open-bldc/open-bldc-hardware/v0.3/power/power.brd

## EAGLE design v0.3/power/power.brd (2012-07-01)

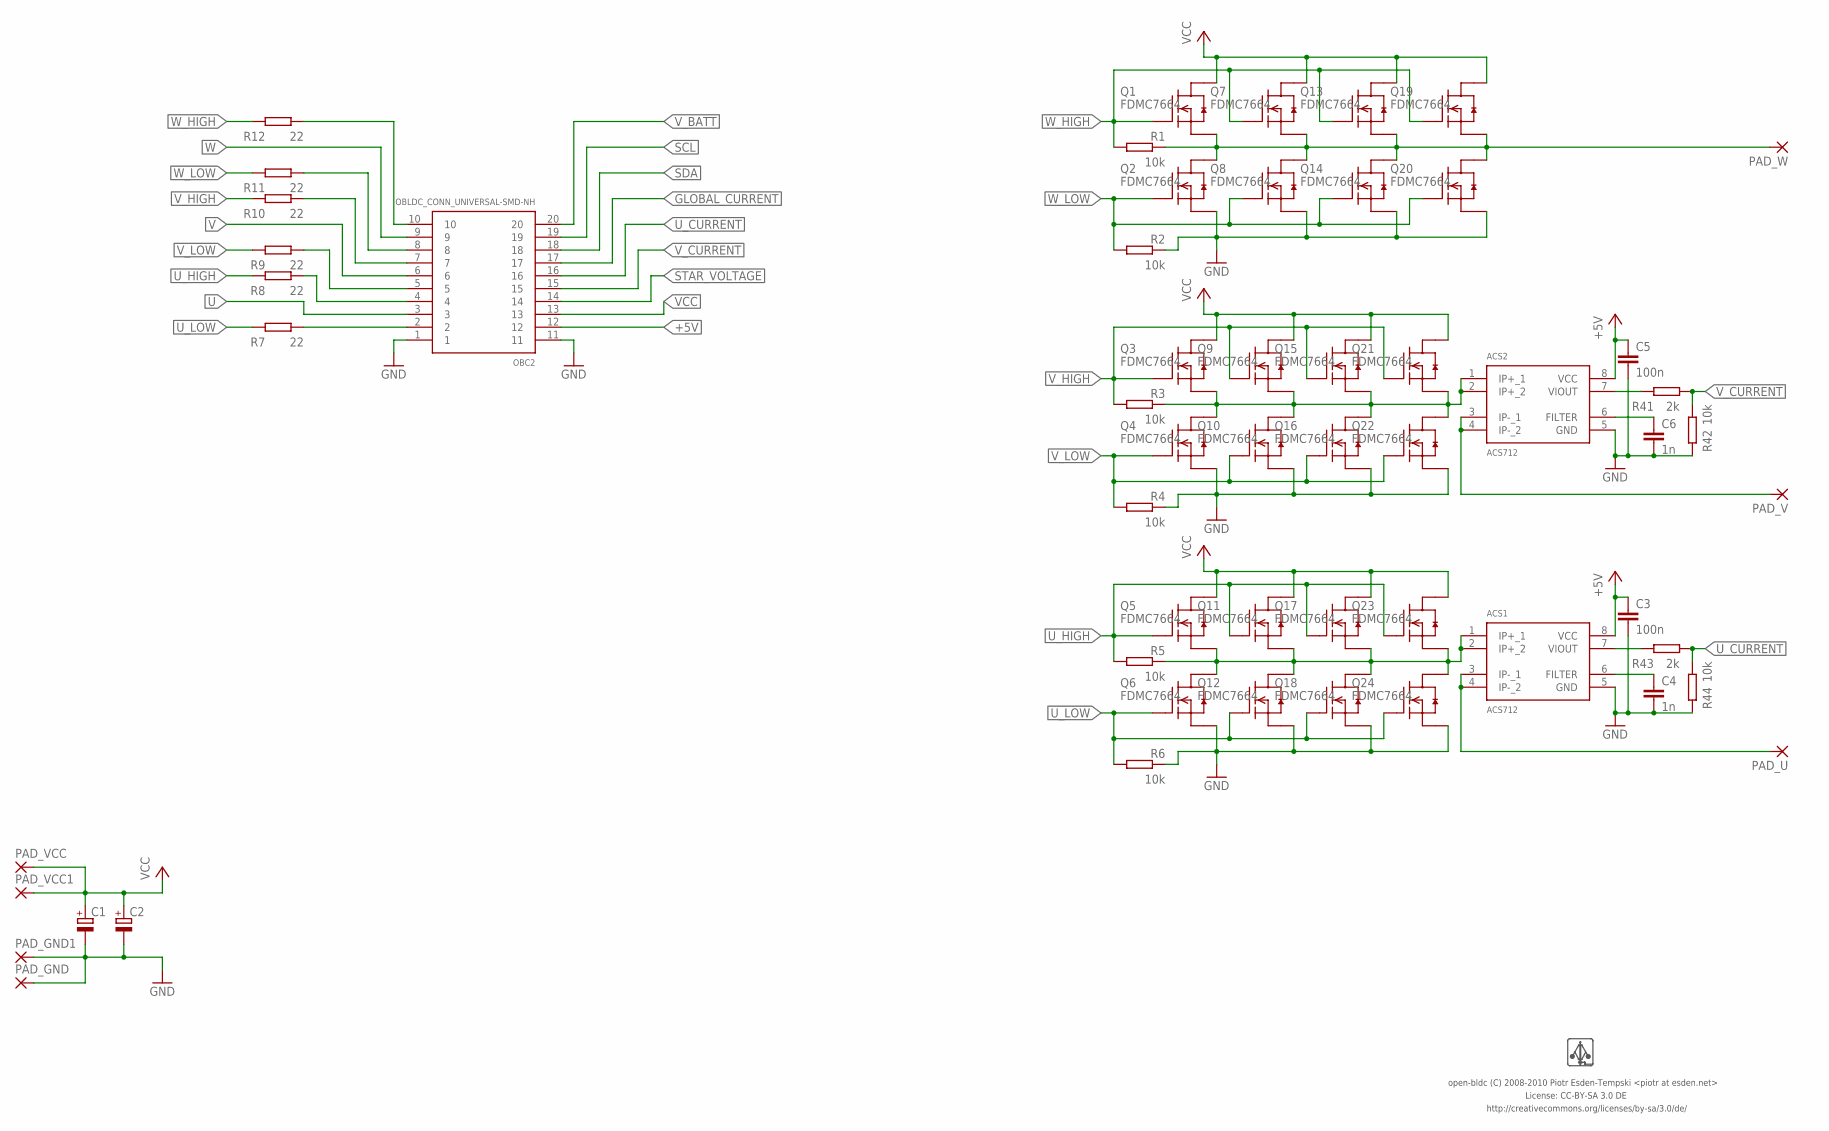
[picture p24: schematic power.sch]

Parts:
ACS1, ACS2: ACS712; SO8
C1, C2: CPOL-EUE5-10.5; E5-10,5
C3, C5: 100n; 0603-CAP
C4, C6: 1n; 0603-CAP
OBC2: OBLDC_CONN_UNIVERSAL-SMD-NH; OBLDC_CONN_SMD_NO_HOLES
PAD_GND, PAD_GND1: WIREPAD-2MM; WIREPAD_2MM
PAD_U: WIREPAD-2MM; WIREPAD_2MM
PAD_V: WIREPAD-2MM; WIREPAD_2MM
PAD_VCC, PAD_VCC1: WIREPAD-2MM; WIREPAD_2MM
PAD_W: WIREPAD-2MM; WIREPAD_2MM
Q1, Q2, Q3, Q4, Q5, Q6, Q7, Q8, Q9, Q10, Q11, Q12, Q13, Q14, Q15, Q16, Q17, Q18, Q19, Q20, Q21, Q22, Q23, Q24: FDMC7664; MLP33
R1, R2, R3, R4, R5, R6, R42, R44: 10k; 0603-RES
R7, R8, R9, R10, R11, R12: 22; 0603-RES
R41, R43: 2k; 0603-RES
U$2: LOGO-NORM; LOGO

Connections:
+5V: ACS1.8 (VCC), ACS2.8 (VCC), C3.P$1 (1), C5.P$1 (1), OBC2.12
GLOBAL_CURRENT: OBC2.17
GND: ACS1.5 (GND), ACS2.5 (GND), C1.-, C2.-, C3.P$2 (2), C4.P$2 (2), C5.P$2 (2), C6.P$2 (2), OBC2.1, OBC2.11, PAD_GND.1, PAD_GND1.1, Q2.123S (S), Q4.123S (S), Q6.123S (S), Q8.123S (S), Q10.123S (S), Q12.123S (S), Q14.123S (S), Q16.123S (S), Q18.123S (S), Q20.123S (S), Q22.123S (S), Q24.123S (S), R2.P$1 (1), R4.P$1 (1), R6.P$1 (1), R42.P$2 (2), R44.P$2 (2)
unnamed: ACS1.3 (IP-_1), ACS1.4 (IP-_2), PAD_U.1
unnamed: ACS2.6 (FILTER), C6.P$1 (1)
unnamed: ACS2.3 (IP-_1), ACS2.4 (IP-_2), PAD_V.1
unnamed: OBC2.2, R7.P$1 (1)
unnamed: OBC2.4, R8.P$1 (1)
unnamed: OBC2.5, R9.P$1 (1)
unnamed: OBC2.7, R10.P$1 (1)
unnamed: OBC2.8, R11.P$1 (1)
unnamed: OBC2.10, R12.P$1 (1)
unnamed: ACS1.6 (FILTER), C4.P$1 (1)
unnamed: ACS2.7 (VIOUT), R41.P$2 (2)
unnamed: ACS1.7 (VIOUT), R43.P$2 (2)
SCL: OBC2.19
SDA: OBC2.18
STAR_VOLTAGE: OBC2.14
U: ACS1.1 (IP+_1), ACS1.2 (IP+_2), OBC2.3, Q5.123S (S), Q6.5678D (D), Q11.123S (S), Q12.5678D (D), Q17.123S (S), Q18.5678D (D), Q23.123S (S), Q24.5678D (D), R5.P$1 (1)
U_CURRENT: OBC2.16, R43.P$1 (1), R44.P$1 (1)
U_HIGH: Q5.4G (G), Q11.4G (G), Q17.4G (G), Q23.4G (G), R5.P$2 (2), R8.P$2 (2)
U_LOW: Q6.4G (G), Q12.4G (G), Q18.4G (G), Q24.4G (G), R6.P$2 (2), R7.P$2 (2)
V: ACS2.1 (IP+_1), ACS2.2 (IP+_2), OBC2.6, Q3.123S (S), Q4.5678D (D), Q9.123S (S), Q10.5678D (D), Q15.123S (S), Q16.5678D (D), Q21.123S (S), Q22.5678D (D), R3.P$1 (1)
VCC: C1.+, C2.+, OBC2.13, PAD_VCC.1, PAD_VCC1.1, Q1.5678D (D), Q3.5678D (D), Q5.5678D (D), Q7.5678D (D), Q9.5678D (D), Q11.5678D (D), Q13.5678D (D), Q15.5678D (D), Q17.5678D (D), Q19.5678D (D), Q21.5678D (D), Q23.5678D (D)
V_BATT: OBC2.20
V_CURRENT: OBC2.15, R41.P$1 (1), R42.P$1 (1)
V_HIGH: Q3.4G (G), Q9.4G (G), Q15.4G (G), Q21.4G (G), R3.P$2 (2), R10.P$2 (2)
V_LOW: Q4.4G (G), Q10.4G (G), Q16.4G (G), Q22.4G (G), R4.P$2 (2), R9.P$2 (2)
W: OBC2.9, PAD_W.1, Q1.123S (S), Q2.5678D (D), Q7.123S (S), Q8.5678D (D), Q13.123S (S), Q14.5678D (D), Q19.123S (S), Q20.5678D (D), R1.P$1 (1)
W_HIGH: Q1.4G (G), Q7.4G (G), Q13.4G (G), Q19.4G (G), R1.P$2 (2), R12.P$2 (2)
W_LOW: Q2.4G (G), Q8.4G (G), Q14.4G (G), Q20.4G (G), R2.P$2 (2), R11.P$2 (2)

Notes on the sheet:
License: CC-BY-SA 3.0 DE
http://creativecommons.org/licenses/by-sa/3.0/de/
open-bldc (C) 2008-2010 Piotr Esden-Tempski <piotr at esden.net>

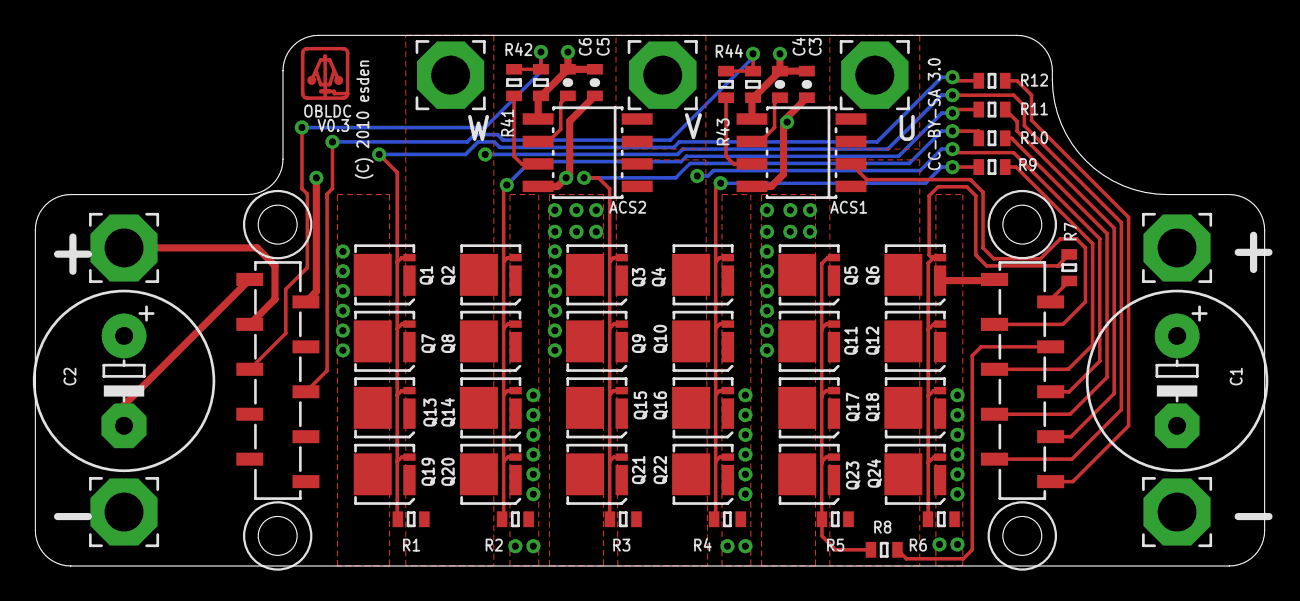
[picture p25: board power.brd from above]

Board: 4 copper layers, 69.5 x 30.0 mm, 58 parts (0 on the bottom side), 26 nets.

Other parts of the board:
U$1: OBLDC_MECH
