open-bldc/open-bldc-hardware/onepiece/v0.1/onepiece.brd

## EAGLE design onepiece/v0.1/onepiece.brd (2012-07-01)

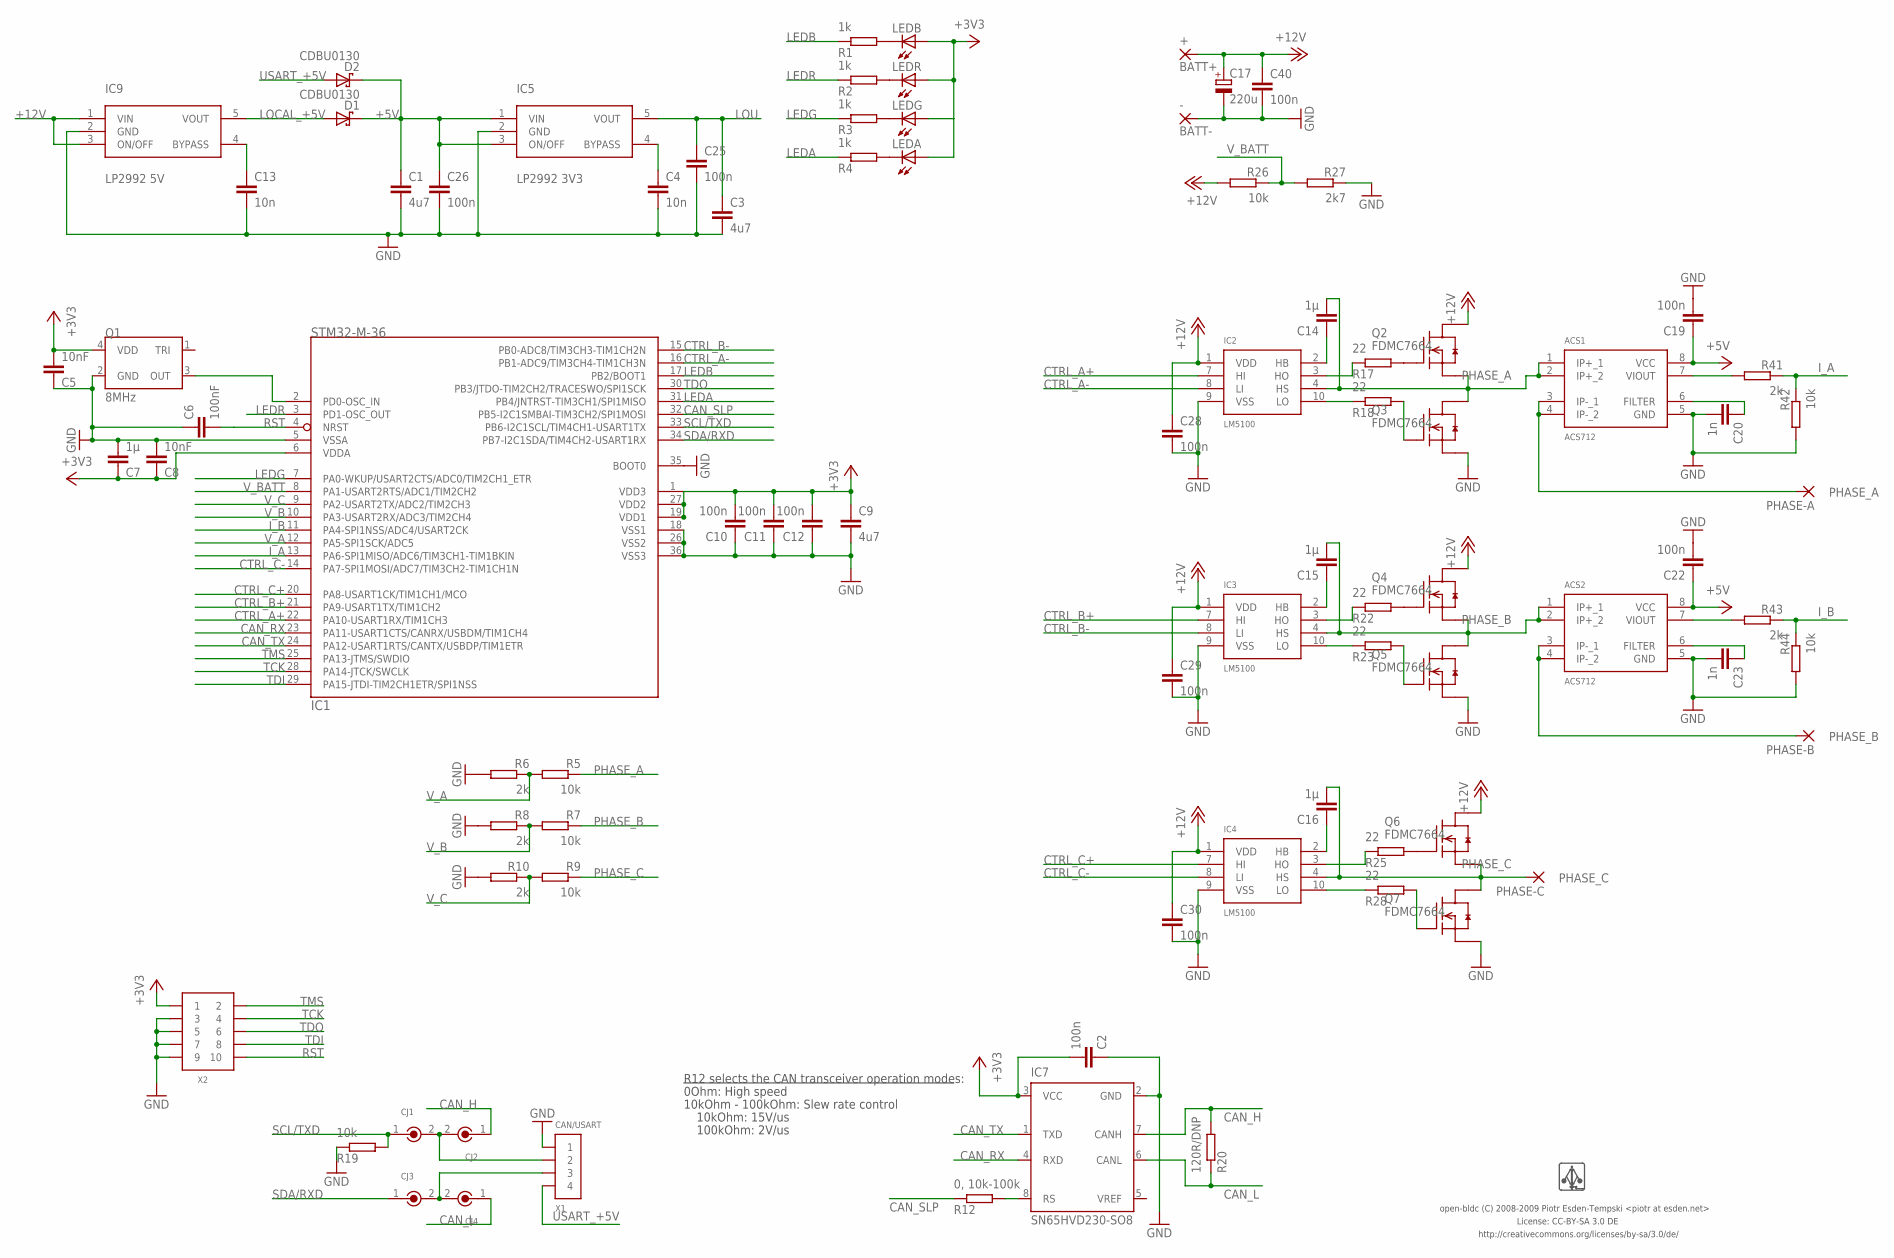
[picture p26: schematic onepiece.sch]

Parts:
+: BATT+; SMD2,54-5,08
-: BATT-; SMD2,54-5,08
ACS1, ACS2: ACS712; SO8
C1, C3, C9: 4u7; 0603-CAP
C2, C10, C11, C12, C19, C22, C25, C26, C28, C29, C30, C40: 100n; 0603-CAP
C4, C13: 10n; 0603-CAP
C5, C8: 10nF; 0603-CAP
C6: 100nF; 0603-CAP
C7, C14, C15, C16: 1µ; 0603-CAP
C17: 220u; 7343/D
C20, C23: 1n; 0603-CAP
CJ1, CJ2, CJ3, CJ4: CIRC_JMP
D1, D2: CDBU0130; 0603-LED
IC1: STM32-M-36; VFQFPN36-LP
IC2, IC3, IC4: LM5100; LLP-10
IC5: LP2992 3V3; SOT23-5
IC7: SN65HVD230-SO8; SO8
IC9: LP2992 5V; SOT23-5
LEDA: AMBER; 0603-LED
LEDB: BLUE; 0603-LED
LEDG: GREEN; 0603-LED
LEDR: RED; 0603-LED
PHASE-A: PHASE_A; SMD2,54-5,08
PHASE-B: PHASE_B; SMD2,54-5,08
PHASE-C: PHASE_C; SMD2,54-5,08
Q1: 8MHz; ASE_OSCILLATOR
Q2, Q3, Q4, Q5, Q6, Q7: FDMC7664; MLP33
R1, R2, R3, R4: 1k; 0603-RES
R5, R7, R9, R19, R26, R42, R44: 10k; 0603-RES
R6, R8, R10, R41, R43: 2k; 0603-RES
R12: 0, 10k-100k; 0603-RES
R17, R18, R22, R23, R25, R28: 22; 0603-RES
R20: 120R/DNP; 0603-RES
R27: 2k7; 0603-RES
U$1: LOGO; LOGO_SMALL
X1: CAN/USART; PB-53261-04
X2: PIN_HDR_EDG_1.27MM_5-2; PIN_HDR_1.27MM_SMD_DH_10

Connections:
+5V: ACS1.8 (VCC), ACS2.8 (VCC), C1.P$1 (1), C19.P$1 (1), C22.P$1 (1), C26.P$1 (1), D1.C, D2.C, IC5.1 (VIN), IC5.3 (ON/OFF)
+12V: +.1, C17.+, C28.P$1 (1), C29.P$1 (1), C30.P$1 (1), C40.P$1 (1), IC2.1 (VDD), IC3.1 (VDD), IC4.1 (VDD), IC9.1 (VIN), IC9.3 (ON/OFF), Q2.5678D (D), Q4.5678D (D), Q6.5678D (D), R26.P$2 (2)
CAN_H: CJ2.1, IC7.7 (CANH), R20.P$2 (2)
CAN_L: CJ4.1, IC7.6 (CANL), R20.P$1 (1)
CAN_RX: IC1.23 (PA11-USART1CTS/CANRX/USBDM/TIM1CH4), IC7.4 (RXD)
CAN_SLP: IC1.32 (PB5-I2C1SMBAI-TIM3CH2/SPI1MOSI), R12.P$1 (1)
CAN_TX: IC1.24 (PA12-USART1RTS/CANTX/USBDP/TIM1ETR), IC7.1 (TXD)
CTRL_A+: IC1.22 (PA10-USART1RX/TIM1CH3), IC2.7 (HI)
CTRL_A-: IC1.16 (PB1-ADC9/TIM3CH4-TIM1CH3N), IC2.8 (LI)
CTRL_B+: IC1.21 (PA9-USART1TX/TIM1CH2), IC3.7 (HI)
CTRL_B-: IC1.15 (PB0-ADC8/TIM3CH3-TIM1CH2N), IC3.8 (LI)
CTRL_C+: IC1.20 (PA8-USART1CK/TIM1CH1/MCO), IC4.7 (HI)
CTRL_C-: IC1.14 (PA7-SPI1MOSI/ADC7/TIM3CH2-TIM1CH1N), IC4.8 (LI)
GND: -.1, ACS1.5 (GND), ACS2.5 (GND), C1.P$2 (2), C2.P$1 (1), C3.P$2 (2), C4.P$2 (2), C5.P$1 (1), C6.P$1 (1), C7.P$2 (2), C8.P$2 (2), C9.P$2 (2), C10.P$1 (1), C11.P$1 (1), C12.P$1 (1), C13.P$2 (2), C17.-, C19.P$2 (2), C20.P$2 (2), C22.P$2 (2), C23.P$2 (2), C25.P$2 (2), C26.P$2 (2), C28.P$2 (2), C29.P$2 (2), C30.P$2 (2), C40.P$2 (2), IC1.5 (VSSA), IC1.18 (VSS1), IC1.26 (VSS2), IC1.35 (BOOT0), IC1.36 (VSS3), IC2.9 (VSS), IC3.9 (VSS), IC4.9 (VSS), IC5.2 (GND), IC7.2 (GND), IC9.2 (GND), Q1.2 (GND), Q3.123S (S), Q5.123S (S), Q7.123S (S), R6.P$2 (2), R8.P$2 (2), R10.P$2 (2), R19.P$1 (1), R27.P$1 (1), R42.P$2 (2), R44.P$2 (2), X1.1, X2.3, X2.5, X2.7, X2.9
I_A: IC1.13 (PA6-SPI1MISO/ADC6/TIM3CH1-TIM1BKIN), R41.P$1 (1), R42.P$1 (1)
I_B: IC1.11 (PA4-SPI1NSS/ADC4/USART2CK), R43.P$1 (1), R44.P$1 (1)
I_PHASE_A: ACS1.3 (IP-_1), ACS1.4 (IP-_2), PHASE-A.1
I_PHASE_B: ACS2.3 (IP-_1), ACS2.4 (IP-_2), PHASE-B.1
LEDA: IC1.31 (PB4/JNTRST-TIM3CH1/SPI1MISO), R4.P$1 (1)
LEDB: IC1.17 (PB2/BOOT1), R1.P$1 (1)
LEDG: IC1.7 (PA0-WKUP/USART2CTS/ADC0/TIM2CH1_ETR), R3.P$1 (1)
LEDR: IC1.3 (PD1-OSC_OUT), R2.P$1 (1)
LOCAL_+5V: D1.A, IC9.5 (VOUT)
LOU: C2.P$2 (2), C3.P$1 (1), C5.P$2 (2), C7.P$1 (1), C8.P$1 (1), C9.P$1 (1), C10.P$2 (2), C11.P$2 (2), C12.P$2 (2), C25.P$1 (1), IC1.1 (VDD3), IC1.6 (VDDA), IC1.19 (VDD1), IC1.27 (VDD2), IC5.5 (VOUT), IC7.3 (VCC), LEDA.A, LEDB.A, LEDG.A, LEDR.A, Q1.4 (VDD), X2.1
unnamed: IC3.3 (HO), R22.P$1 (1)
unnamed: IC2.3 (HO), R17.P$1 (1)
unnamed: LEDB.C, R1.P$2 (2)
unnamed: C4.P$1 (1), IC5.4 (BYPASS)
unnamed: LEDG.C, R3.P$2 (2)
unnamed: C13.P$1 (1), IC9.4 (BYPASS)
unnamed: IC2.10 (LO), R18.P$1 (1)
unnamed: IC7.8 (RS), R12.P$2 (2)
unnamed: CJ3.2, CJ4.2, X1.3
unnamed: LEDR.C, R2.P$2 (2)
unnamed: Q2.4G (G), R17.P$2 (2)
unnamed: C14.P$1 (1), IC2.2 (HB)
unnamed: IC3.10 (LO), R23.P$1 (1)
unnamed: Q4.4G (G), R22.P$2 (2)
unnamed: Q6.4G (G), R25.P$2 (2)
unnamed: C15.P$1 (1), IC3.2 (HB)
unnamed: Q5.4G (G), R23.P$2 (2)
unnamed: IC4.3 (HO), R25.P$1 (1)
unnamed: IC4.10 (LO), R28.P$1 (1)
unnamed: C16.P$1 (1), IC4.2 (HB)
unnamed: LEDA.C, R4.P$2 (2)
unnamed: CJ1.2, CJ2.2, X1.2
unnamed: Q7.4G (G), R28.P$2 (2)
unnamed: ACS1.6 (FILTER), C20.P$1 (1)
unnamed: ACS1.7 (VIOUT), R41.P$2 (2)
unnamed: ACS2.6 (FILTER), C23.P$1 (1)
unnamed: ACS2.7 (VIOUT), R43.P$2 (2)
unnamed: IC1.2 (PD0-OSC_IN), Q1.3 (OUT)
unnamed: Q3.4G (G), R18.P$2 (2)
PHASE_A: ACS1.1 (IP+_1), ACS1.2 (IP+_2), C14.P$2 (2), IC2.4 (HS), Q2.123S (S), Q3.5678D (D), R5.P$1 (1)
PHASE_B: ACS2.1 (IP+_1), ACS2.2 (IP+_2), C15.P$2 (2), IC3.4 (HS), Q4.123S (S), Q5.5678D (D), R7.P$1 (1)
PHASE_C: C16.P$2 (2), IC4.4 (HS), PHASE-C.1, Q6.123S (S), Q7.5678D (D), R9.P$1 (1)
RST: C6.P$2 (2), IC1.4 (NRST), X2.10
SCL/TXD: CJ1.1, IC1.33 (PB6-I2C1SCL/TIM4CH1-USART1TX), R19.P$2 (2)
SDA/RXD: CJ3.1, IC1.34 (PB7-I2C1SDA/TIM4CH2-USART1RX)
TCK: IC1.28 (PA14-JTCK/SWCLK), X2.4
TDI: IC1.29 (PA15-JTDI-TIM2CH1ETR/SPI1NSS), X2.8
TDO: IC1.30 (PB3/JTDO-TIM2CH2/TRACESWO/SPI1SCK), X2.6
TMS: IC1.25 (PA13-JTMS/SWDIO), X2.2
USART_+5V: D2.A, X1.4
V_A: IC1.12 (PA5-SPI1SCK/ADC5), R5.P$2 (2), R6.P$1 (1)
V_B: IC1.10 (PA3-USART2RX/ADC3/TIM2CH4), R7.P$2 (2), R8.P$1 (1)
V_BATT: IC1.8 (PA1-USART2RTS/ADC1/TIM2CH2), R26.P$1 (1), R27.P$2 (2)
V_C: IC1.9 (PA2-USART2TX/ADC2/TIM2CH3), R9.P$2 (2), R10.P$1 (1)

Notes on the sheet:
License: CC-BY-SA 3.0 DE
http://creativecommons.org/licenses/by-sa/3.0/de/
open-bldc (C) 2008-2009 Piotr Esden-Tempski <piotr at esden.net>
R12 selects the CAN transceiver operation modes:
0Ohm: High speed
10kOhm - 100kOhm: Slew rate control
10kOhm: 15V/us
100kOhm: 2V/us

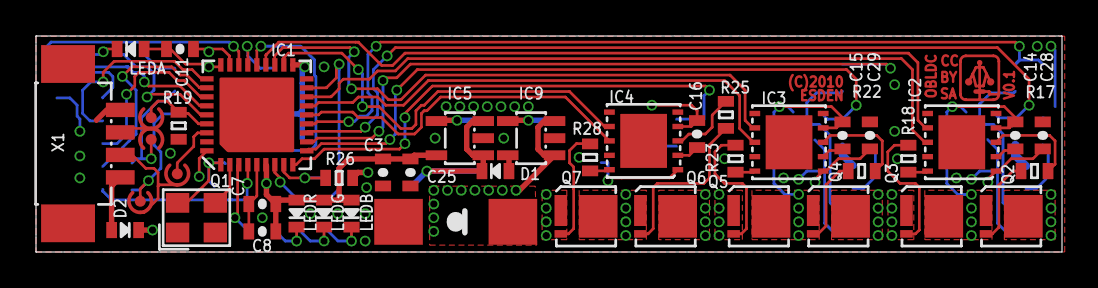
[picture p27: board onepiece.brd from above]

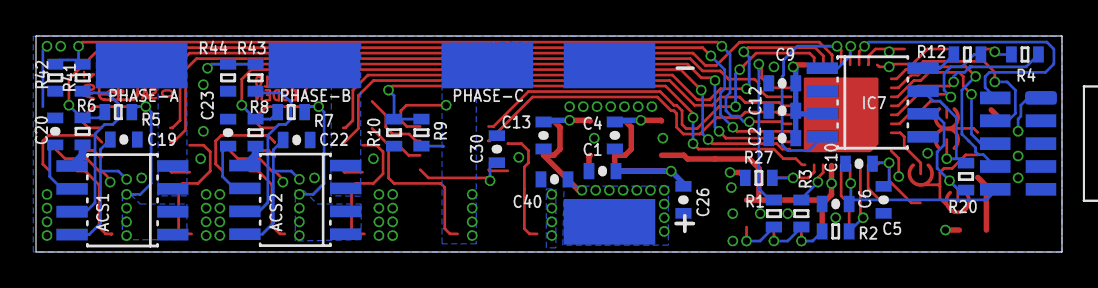
[picture p28: board onepiece.brd from below]

Board: 4 copper layers, 57.0 x 12.0 mm, 86 parts (42 on the bottom side), 68 nets.
