open-bldc/open-bldc-hardware/v0.3/power_driver/power_driver.brd

## EAGLE design v0.3/power_driver/power_driver.brd (2012-07-01)

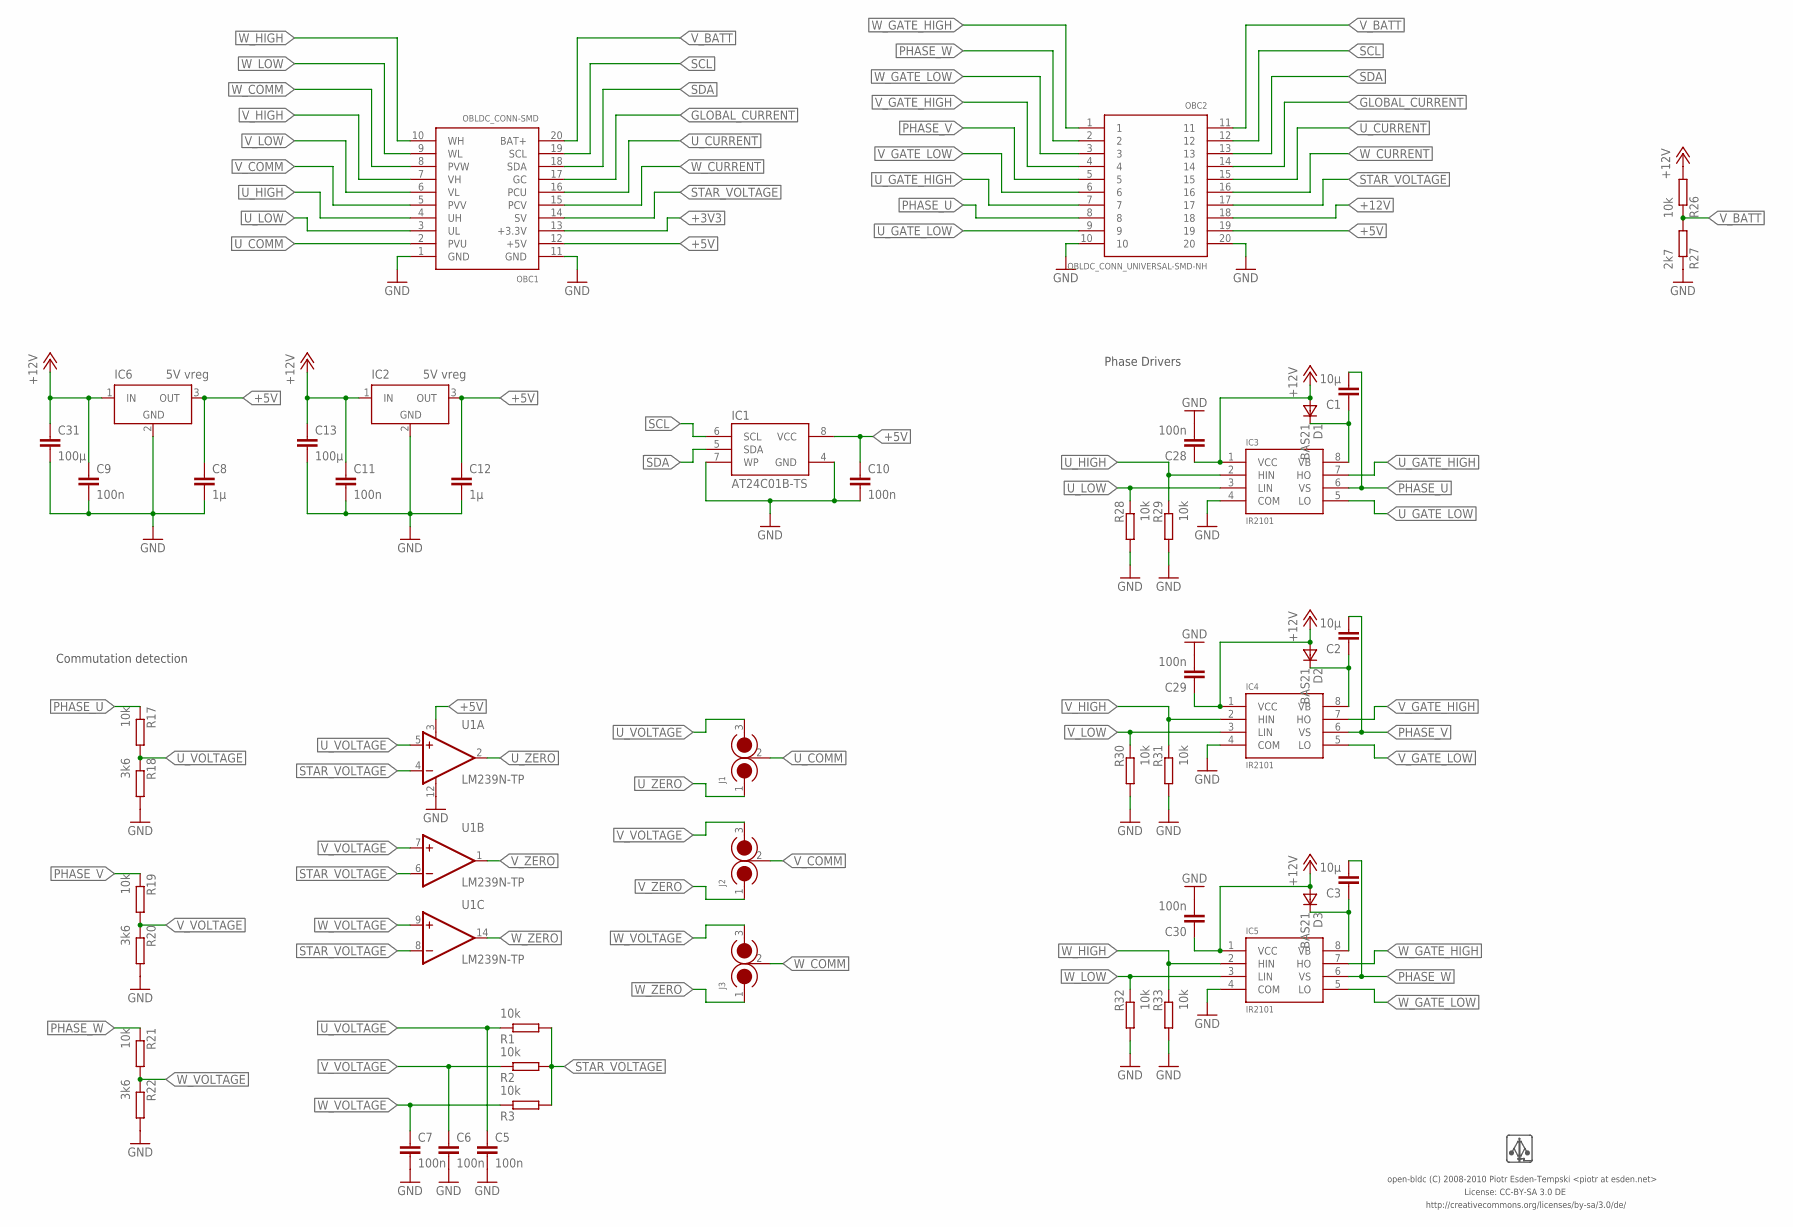
[picture p29: schematic power_driver.sch]

Parts:
C1, C2, C3: 10µ; 0603-CAP
C5, C6, C7, C9, C10, C11, C28, C29, C30: 100n; 0603-CAP
C8, C12: 1µ; 0603-CAP
C13, C31: 100µ; 0603-CAP
D1, D2, D3: BAS21; SOT-23
IC1: AT24C01B-TS; TSSOP8
IC2, IC6: 5V vreg; SOT223
IC3, IC4, IC5: IR2101; SO-8
J1, J2, J3: CIRC_JMP_2
OBC1: OBLDC_CONN-SMD; OBLDC_CONN_SMD
OBC2: OBLDC_CONN_UNIVERSAL-SMD-NH; OBLDC_CONN_SMD_NO_HOLES
R1, R2, R3, R17, R19, R21, R26, R28, R29, R30, R31, R32, R33: 10k; 0603-RES
R18, R20, R22: 3k6; 0603-RES
R27: 2k7; 0603-RES
U1: LM239N-TP; TSSOP_14
U$1: LOGO-NORM; LOGO

Connections:
+3V3: OBC1.13 (+3.3V)
+5V: C8.P$1 (1), C10.P$1 (1), C12.P$1 (1), IC1.8 (VCC), IC2.3 (OUT), IC6.3 (OUT), OBC1.12 (+5V), OBC2.19, U1.3 (V+)
+12V: C9.P$1 (1), C11.P$1 (1), C13.P$1 (1), C28.P$1 (1), C29.P$1 (1), C30.P$1 (1), C31.P$1 (1), D1.3 (A), D2.3 (A), D3.3 (A), IC2.1 (IN), IC3.1 (VCC), IC4.1 (VCC), IC5.1 (VCC), IC6.1 (IN), OBC2.18, R26.P$2 (2)
GLOBAL_CURRENT: OBC1.17 (GC), OBC2.14
GND: C5.P$2 (2), C6.P$2 (2), C7.P$2 (2), C8.P$2 (2), C9.P$2 (2), C10.P$2 (2), C11.P$2 (2), C12.P$2 (2), C13.P$2 (2), C28.P$2 (2), C29.P$2 (2), C30.P$2 (2), C31.P$2 (2), IC1.4 (GND), IC1.7 (WP), IC2.2 (GND), IC2.4 (GND), IC3.4 (COM), IC4.4 (COM), IC5.4 (COM), IC6.2 (GND), IC6.4 (GND), OBC1.1 (GND), OBC1.11 (GND), OBC2.10, OBC2.20, R18.P$2 (2), R20.P$2 (2), R22.P$2 (2), R27.P$1 (1), R28.P$2 (2), R29.P$2 (2), R30.P$2 (2), R31.P$2 (2), R32.P$2 (2), R33.P$2 (2), U1.12 (V-)
unnamed: C1.P$1 (1), D1.1 (C), IC3.8 (VB)
unnamed: C2.P$1 (1), D2.1 (C), IC4.8 (VB)
unnamed: C3.P$1 (1), D3.1 (C), IC5.8 (VB)
PHASE_U: C1.P$2 (2), IC3.6 (VS), OBC2.8, R17.P$1 (1)
PHASE_V: C2.P$2 (2), IC4.6 (VS), OBC2.5, R19.P$1 (1)
PHASE_W: C3.P$2 (2), IC5.6 (VS), OBC2.2, R21.P$1 (1)
SCL: IC1.6 (SCL), OBC1.19 (SCL), OBC2.12
SDA: IC1.5 (SDA), OBC1.18 (SDA), OBC2.13
STAR_VOLTAGE: OBC1.14 (SV), OBC2.17, R1.P$2 (2), R2.P$2 (2), R3.P$2 (2), U1.4 (-IN), U1.6 (-IN), U1.8 (-IN)
U_COMM: J1.2, OBC1.2 (PVU)
U_CURRENT: OBC1.16 (PCU), OBC2.15
U_GATE_HIGH: IC3.7 (HO), OBC2.7
U_GATE_LOW: IC3.5 (LO), OBC2.9
U_HIGH: IC3.2 (HIN), OBC1.4 (UH), R29.P$1 (1)
U_LOW: IC3.3 (LIN), OBC1.3 (UL), R28.P$1 (1)
U_VOLTAGE: C5.P$1 (1), J1.3, R1.P$1 (1), R17.P$2 (2), R18.P$1 (1), U1.5 (+IN)
U_ZERO: J1.1, U1.2 (OUT)
V_BATT: OBC1.20 (BAT+), OBC2.11, R26.P$1 (1), R27.P$2 (2)
V_COMM: J2.2, OBC1.5 (PVV)
V_GATE_HIGH: IC4.7 (HO), OBC2.4
V_GATE_LOW: IC4.5 (LO), OBC2.6
V_HIGH: IC4.2 (HIN), OBC1.7 (VH), R31.P$1 (1)
V_LOW: IC4.3 (LIN), OBC1.6 (VL), R30.P$1 (1)
V_VOLTAGE: C6.P$1 (1), J2.3, R2.P$1 (1), R19.P$2 (2), R20.P$1 (1), U1.7 (+IN)
V_ZERO: J2.1, U1.1 (OUT)
W_COMM: J3.2, OBC1.8 (PVW)
W_CURRENT: OBC1.15 (PCV), OBC2.16
W_GATE_HIGH: IC5.7 (HO), OBC2.1
W_GATE_LOW: IC5.5 (LO), OBC2.3
W_HIGH: IC5.2 (HIN), OBC1.10 (WH), R33.P$1 (1)
W_LOW: IC5.3 (LIN), OBC1.9 (WL), R32.P$1 (1)
W_VOLTAGE: C7.P$1 (1), J3.3, R3.P$1 (1), R21.P$2 (2), R22.P$1 (1), U1.9 (+IN)
W_ZERO: J3.1, U1.14 (OUT)

Notes on the sheet:
Phase Drivers
License: CC-BY-SA 3.0 DE
http://creativecommons.org/licenses/by-sa/3.0/de/
Commutation detection
open-bldc (C) 2008-2010 Piotr Esden-Tempski <piotr at esden.net>

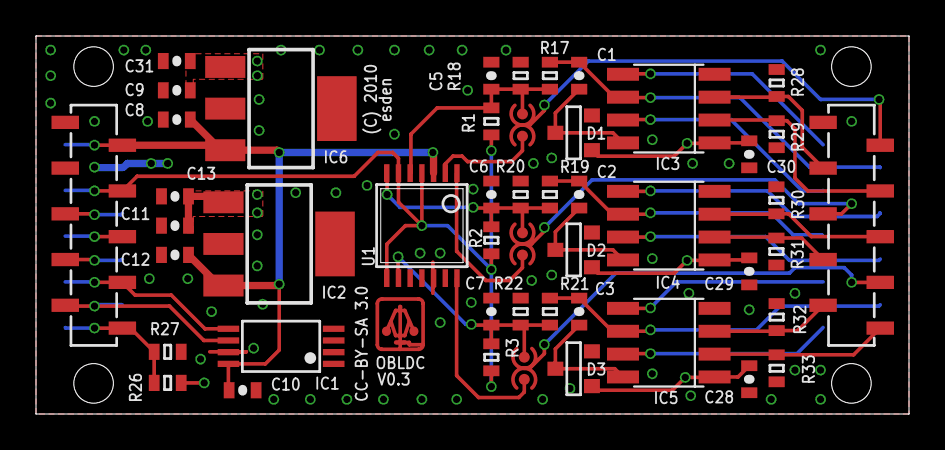
[picture p30: board power_driver.brd from above]

Board: 4 copper layers, 48.5 x 21.0 mm, 49 parts (1 on the bottom side), 37 nets.
