open-bldc/open-bldc-hardware/cpico_power/v0.1/cpico_power.brd

## EAGLE design cpico_power/v0.1/cpico_power.brd (2012-07-01)

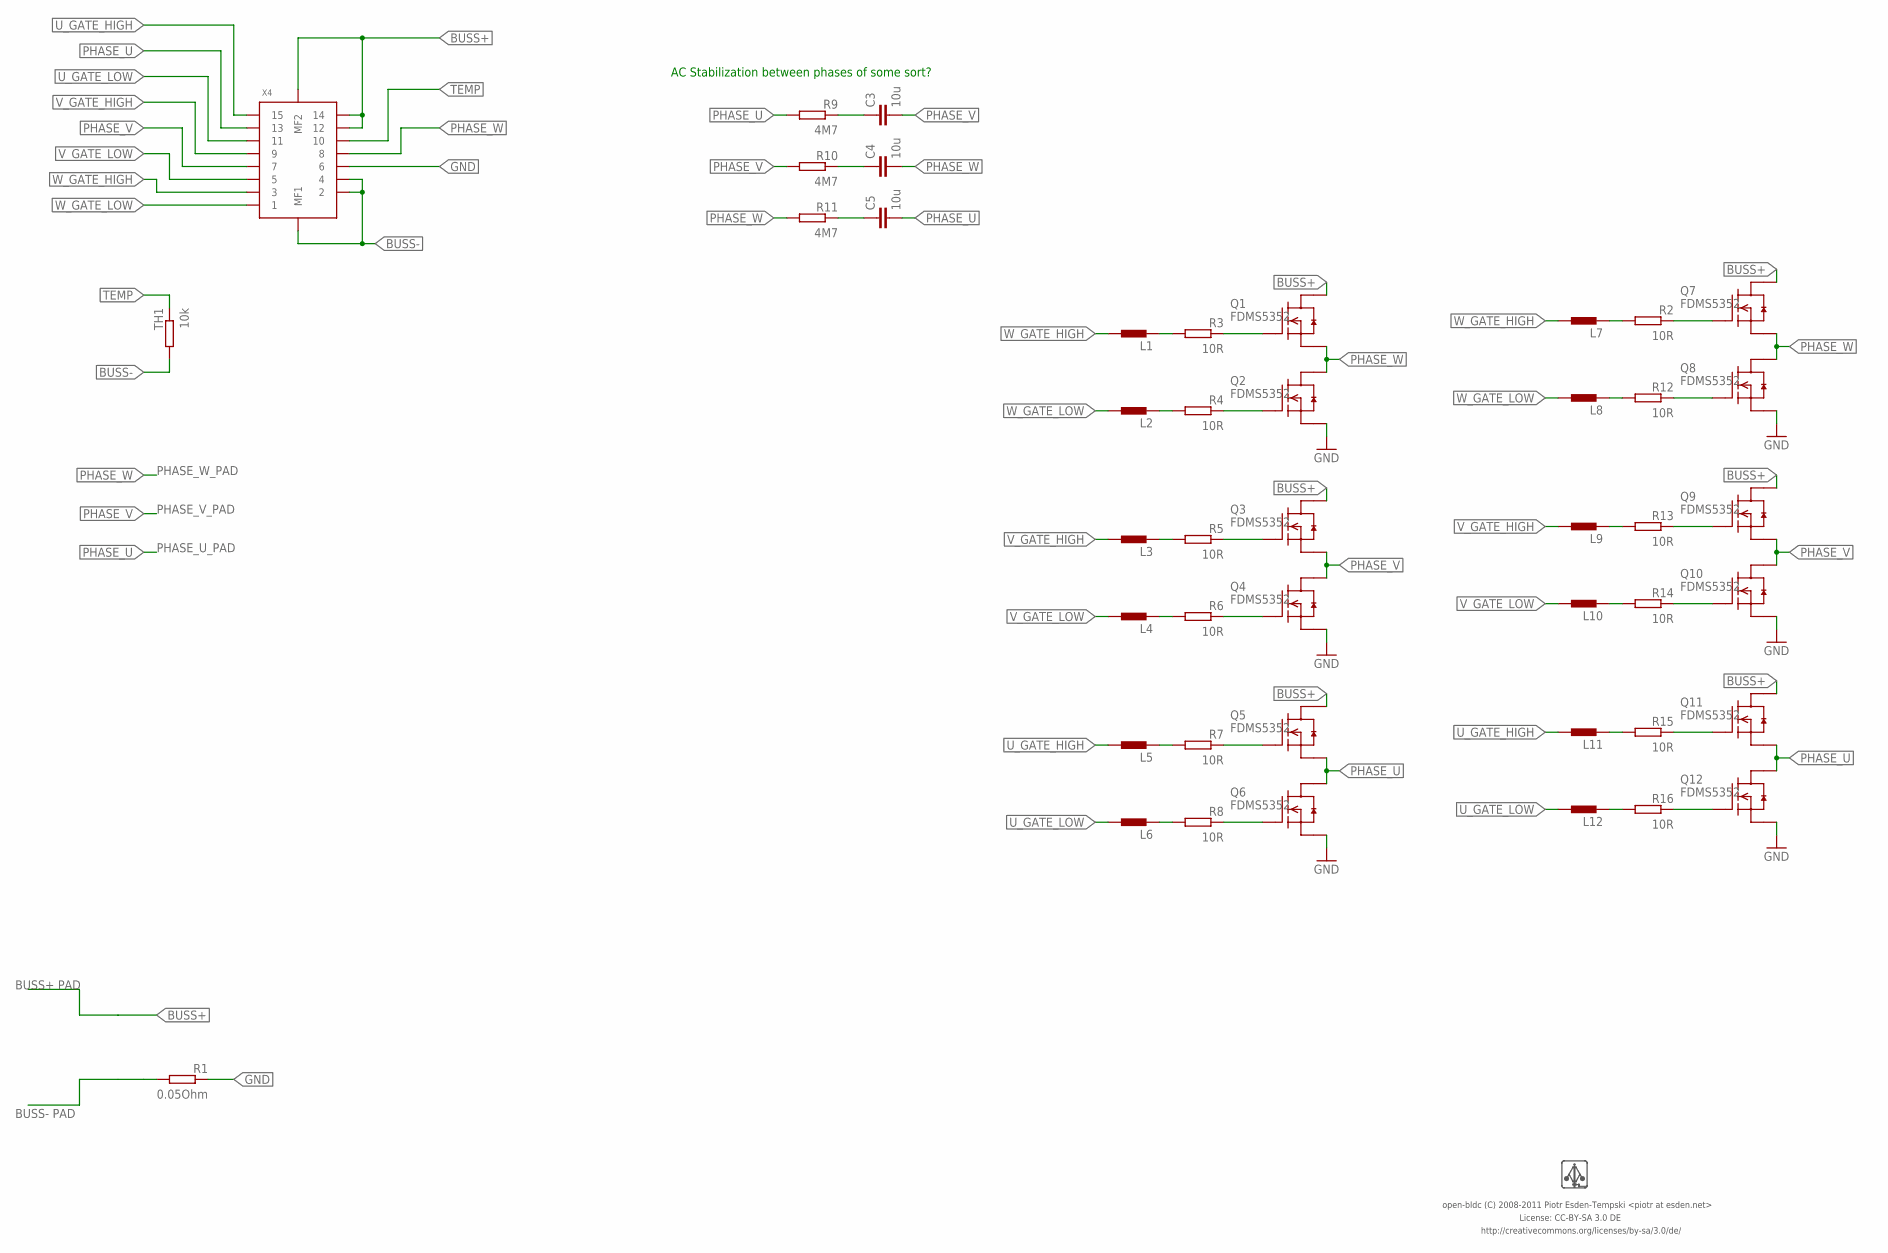
[picture p31: schematic cpico_power.sch]

Parts:
C3, C4, C5: 10u; 0603-CAP
L1, L2, L3, L4, L5, L6, L7, L8, L9, L10, L11, L12: INDUCTOR-0402; 0402-IND
Q1, Q2, Q3, Q4, Q5, Q6, Q7, Q8, Q9, Q10, Q11, Q12: FDMS5352; MSL1
R1: 0.05Ohm; 1206-RES
R2, R3, R4, R5, R6, R7, R8, R12, R13, R14, R15, R16: 10R; 0402-RES
R9, R10, R11: 4M7; 0603-RES
TH1: 10k; 0603-RES
U$2: LOGO-NORM; LOGO
X4: CONN_15-2-2MT-DF9; DF9-15

Connections:
BUSS+: Q1.3 (D), Q3.3 (D), Q5.3 (D), Q7.3 (D), Q9.3 (D), Q11.3 (D), X4.12, X4.14, X4.MF2
BUSS-: R1.P$2 (2), TH1.P$2 (2), X4.2, X4.4, X4.MF1
GND: Q2.1 (S), Q4.1 (S), Q6.1 (S), Q8.1 (S), Q10.1 (S), Q12.1 (S), R1.P$1 (1), X4.6
unnamed: Q1.2 (G), R3.P$1 (1)
unnamed: C3.P$1 (1), R9.P$1 (1)
unnamed: C4.P$1 (1), R10.P$1 (1)
unnamed: C5.P$1 (1), R11.P$1 (1)
unnamed: Q2.2 (G), R4.P$1 (1)
unnamed: Q3.2 (G), R5.P$1 (1)
unnamed: Q4.2 (G), R6.P$1 (1)
unnamed: Q5.2 (G), R7.P$1 (1)
unnamed: Q6.2 (G), R8.P$1 (1)
unnamed: L1.P$2 (2), R3.P$2 (2)
unnamed: L2.P$2 (2), R4.P$2 (2)
unnamed: L3.P$2 (2), R5.P$2 (2)
unnamed: L4.P$2 (2), R6.P$2 (2)
unnamed: L5.P$2 (2), R7.P$2 (2)
unnamed: L6.P$2 (2), R8.P$2 (2)
unnamed: L7.P$2 (2), R2.P$2 (2)
unnamed: L8.P$2 (2), R12.P$2 (2)
unnamed: L9.P$2 (2), R13.P$2 (2)
unnamed: L10.P$2 (2), R14.P$2 (2)
unnamed: L11.P$2 (2), R15.P$2 (2)
unnamed: L12.P$2 (2), R16.P$2 (2)
unnamed: Q7.2 (G), R2.P$1 (1)
unnamed: Q8.2 (G), R12.P$1 (1)
unnamed: Q9.2 (G), R13.P$1 (1)
unnamed: Q10.2 (G), R14.P$1 (1)
unnamed: Q11.2 (G), R15.P$1 (1)
unnamed: Q12.2 (G), R16.P$1 (1)
PHASE_U: C5.P$2 (2), Q5.1 (S), Q6.3 (D), Q11.1 (S), Q12.3 (D), R9.P$2 (2), X4.13
PHASE_V: C3.P$2 (2), Q3.1 (S), Q4.3 (D), Q9.1 (S), Q10.3 (D), R10.P$2 (2), X4.7
PHASE_W: C4.P$2 (2), Q1.1 (S), Q2.3 (D), Q7.1 (S), Q8.3 (D), R11.P$2 (2), X4.8
TEMP: TH1.P$1 (1), X4.10
U_GATE_HIGH: L5.P$1 (1), L11.P$1 (1), X4.15
U_GATE_LOW: L6.P$1 (1), L12.P$1 (1), X4.11
V_GATE_HIGH: L3.P$1 (1), L9.P$1 (1), X4.9
V_GATE_LOW: L4.P$1 (1), L10.P$1 (1), X4.5
W_GATE_HIGH: L1.P$1 (1), L7.P$1 (1), X4.3
W_GATE_LOW: L2.P$1 (1), L8.P$1 (1), X4.1

Notes on the sheet:
License: CC-BY-SA 3.0 DE
http://creativecommons.org/licenses/by-sa/3.0/de/
open-bldc (C) 2008-2011 Piotr Esden-Tempski <piotr at esden.net>
AC Stabilization between phases of some sort?
BUSS+ PAD
BUSS- PAD
PHASE_W_PAD
PHASE_V_PAD
PHASE_U_PAD

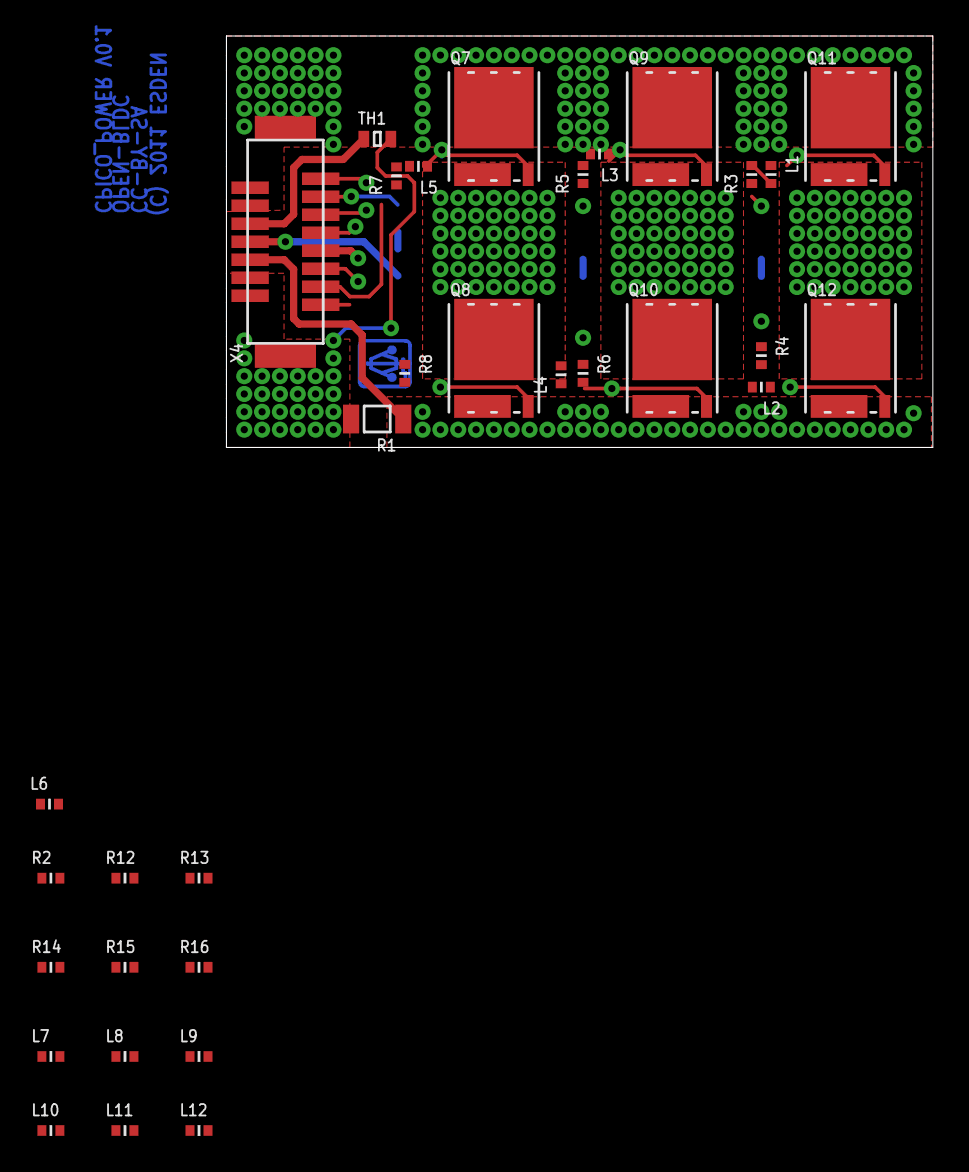
[picture p32: board cpico_power.brd from above]

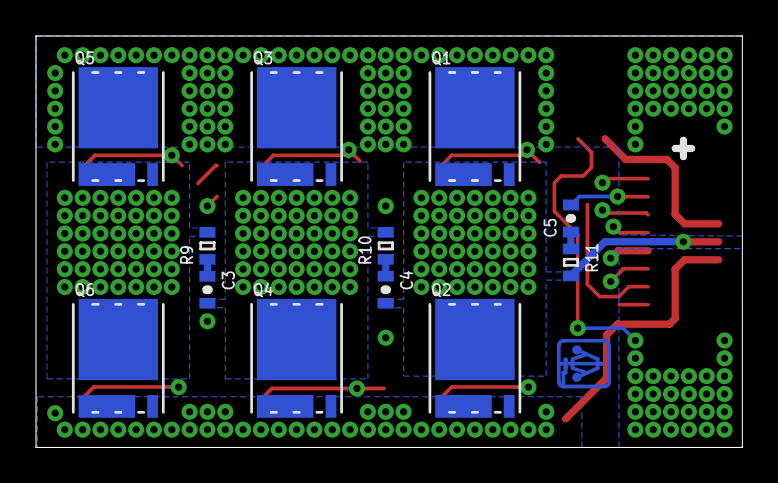
[picture p33: board cpico_power.brd from below]

Board: 4 copper layers, 39.2 x 22.9 mm, 46 parts (13 on the bottom side), 40 nets.
